markusbart82/Homeassistant_MQTT_Light/include/colorhandler.h

#ifndef COLORHANDLER_H
#define COLORHANDLER_H

#include <Arduino.h>

// LED strip white color temperatures in Kelvin
#define WW_TEMP 2300
#define CW_TEMP 7000


class Colorhandler{
  
  private:
    static constexpr uint16_t pwmTableR[256] = {0,16,32,48,64,80,96,112,128,144,160,176,192,208,224,240,256,272,288,304,320,336,352,368,384,400,416,432,448,464,480,496,512,528,544,560,576,592,608,624,640,656,672,688,704,720,736,752,768,784,800,816,832,848,864,880,896,912,928,944,960,976,992,1008,1024,1040,1056,1072,1088,1104,1120,1136,1152,1168,1184,1200,1216,1232,1248,1264,1280,1296,1312,1328,1344,1360,1376,1392,1408,1424,1440,1456,1472,1488,1504,1520,1536,1552,1568,1584,1600,1616,1632,1648,1664,1680,1696,1712,1728,1744,1760,1776,1792,1808,1824,1840,1856,1872,1888,1904,1920,1936,1952,1968,1984,2000,2016,2032,2048,2064,2080,2096,2112,2128,2144,2160,2176,2192,2208,2224,2240,2256,2272,2288,2304,2320,2336,2352,2368,2384,2400,2416,2432,2448,2464,2480,2496,2512,2528,2544,2560,2576,2592,2608,2624,2640,2656,2672,2688,2704,2720,2736,2752,2768,2784,2800,2816,2832,2848,2864,2880,2896,2912,2928,2944,2960,2976,2992,3008,3024,3040,3056,3072,3088,3104,3120,3136,3152,3168,3184,3200,3216,3232,3248,3264,3280,3296,3312,3328,3344,3360,3376,3392,3408,3424,3440,3456,3472,3488,3504,3520,3536,3552,3568,3584,3600,3616,3632,3648,3664,3680,3696,3712,3728,3744,3760,3776,3792,3808,3824,3840,3856,3872,3888,3904,3920,3936,3952,3968,3984,4000,4016,4032,4048,4064,4095};
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
    static void rgbww12ToRgbww8(uint16_t r1, uint16_t g1, uint16_t b1, uint16_t ww1, uint16_t cw1, uint8_t &r2, uint8_t &g2, uint8_t &b2, uint8_t &ww2, uint8_t &cw2);
    
    // translate single 12 bit to 8 bit value
    static uint8_t s12to8(uint16_t in, const uint16_t *pwmTable);
};

#endif
