markusbart82/Homeassistant_MQTT_Light/include/secrets.h

/* all the stuff that shouldn't be shared */

const char* SSID = "YOUR WIFI SSID";
const char* PSK = "YOUR WIFI PASSWORD";
const char* MQTT_BROKER = "BROKER IP OR HOSTNAME";
const char* MQTT_USER = "MQTT BROKER USERNAME";
const char* MQTT_PASS = "MQTT BROKER PASSWORD";
